crjens/PiPowerMeter/Documentation/ACIn.jpg

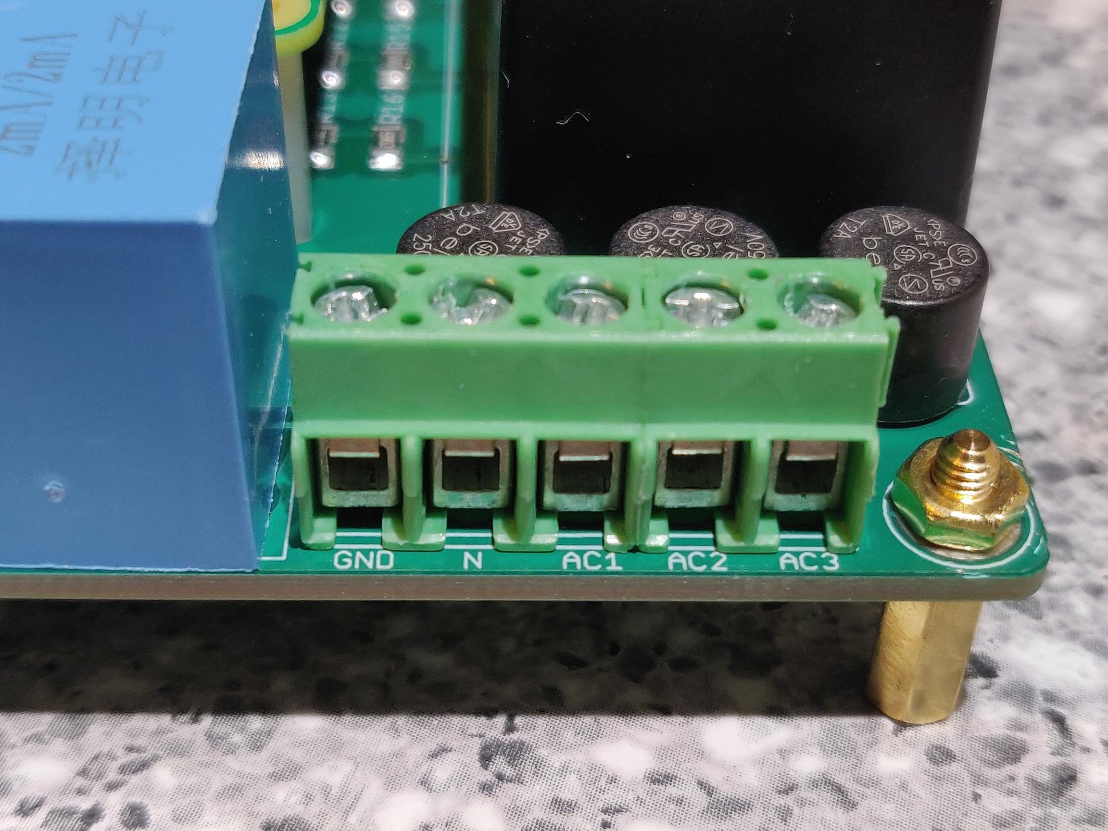
Documentation/ACIn.jpg
