crjens/PiPowerMeter/Documentation/boards.jpg

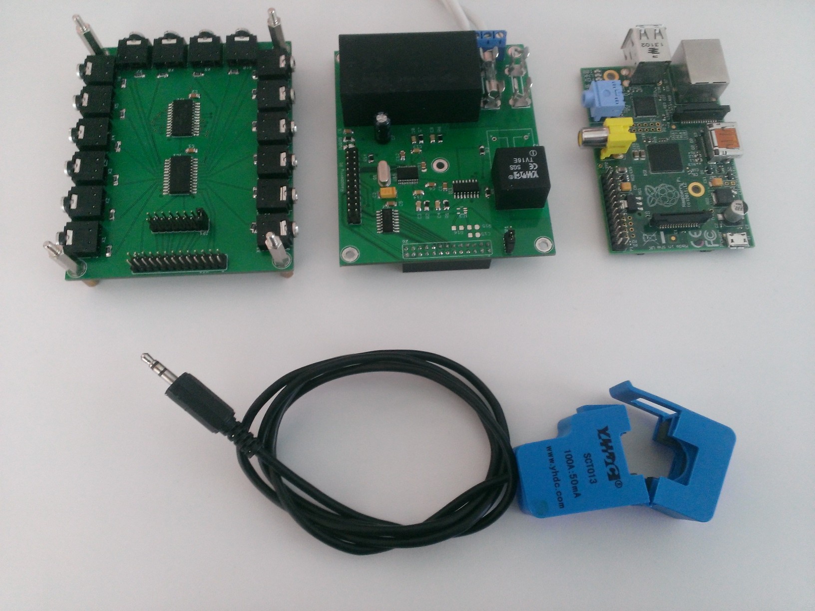
Documentation/boards.jpg
