crjens/PiPowerMeter/Documentation/DSC_0002.JPG

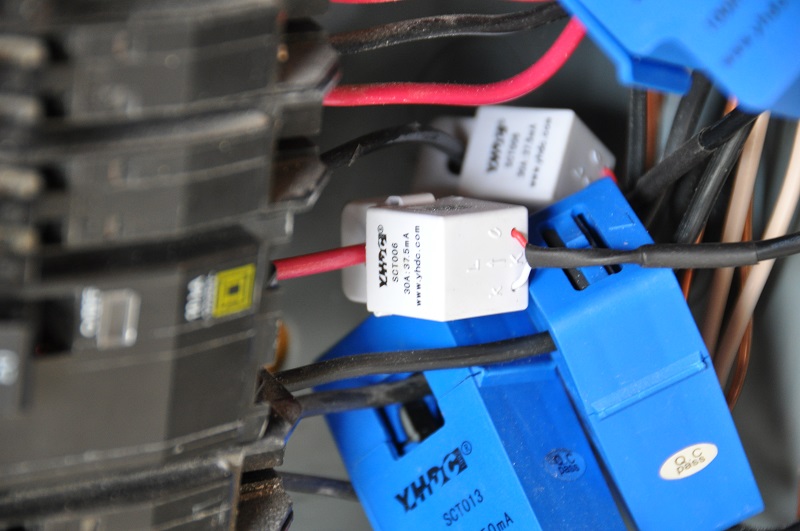
Documentation/DSC_0002.JPG
