crjens/PiPowerMeter/Documentation/DSC_0012.JPG

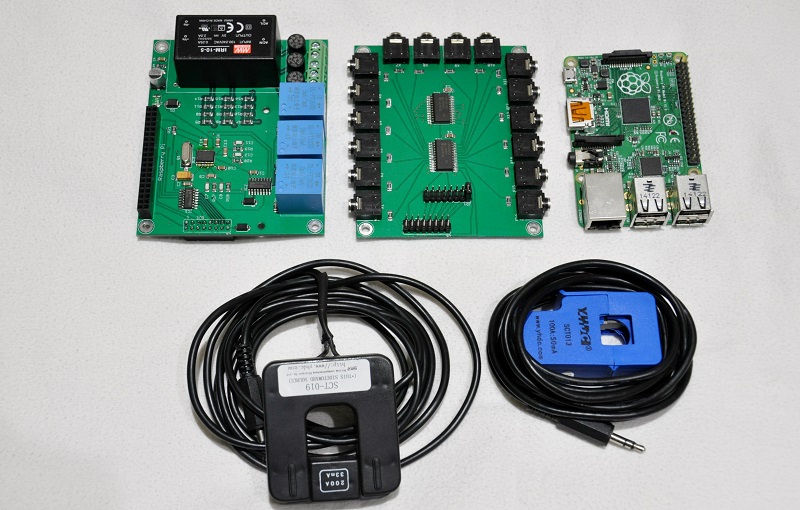
Documentation/DSC_0012.JPG
