crjens/PiPowerMeter/Documentation/DSC_0077.JPG

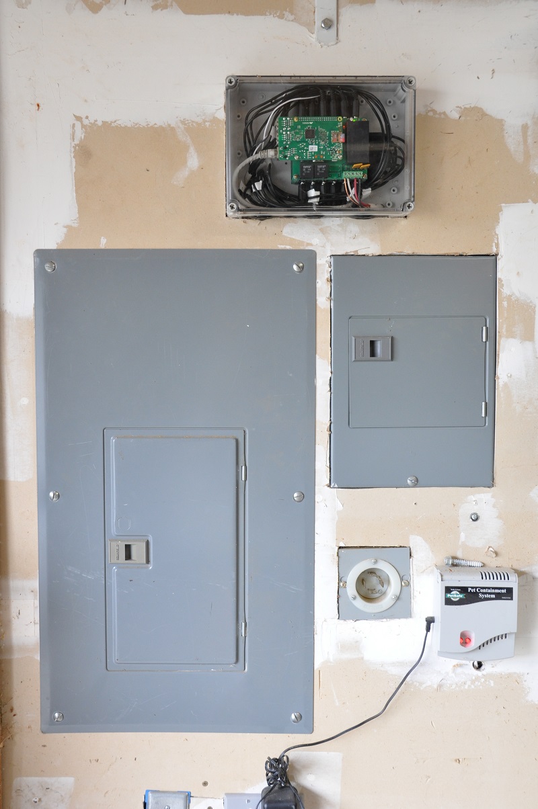
Documentation/DSC_0077.JPG
