crjens/PiPowerMeter/Documentation/DSC_0078.JPG

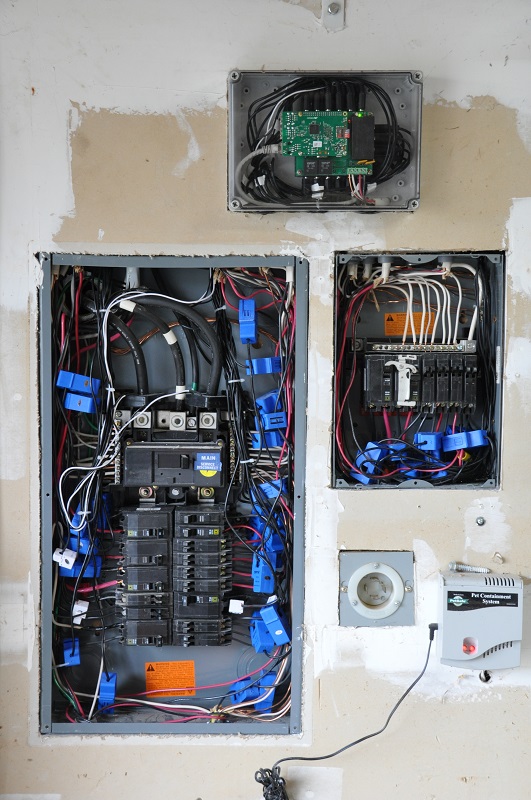
Documentation/DSC_0078.JPG
