crjens/PiPowerMeter/Documentation/main.png

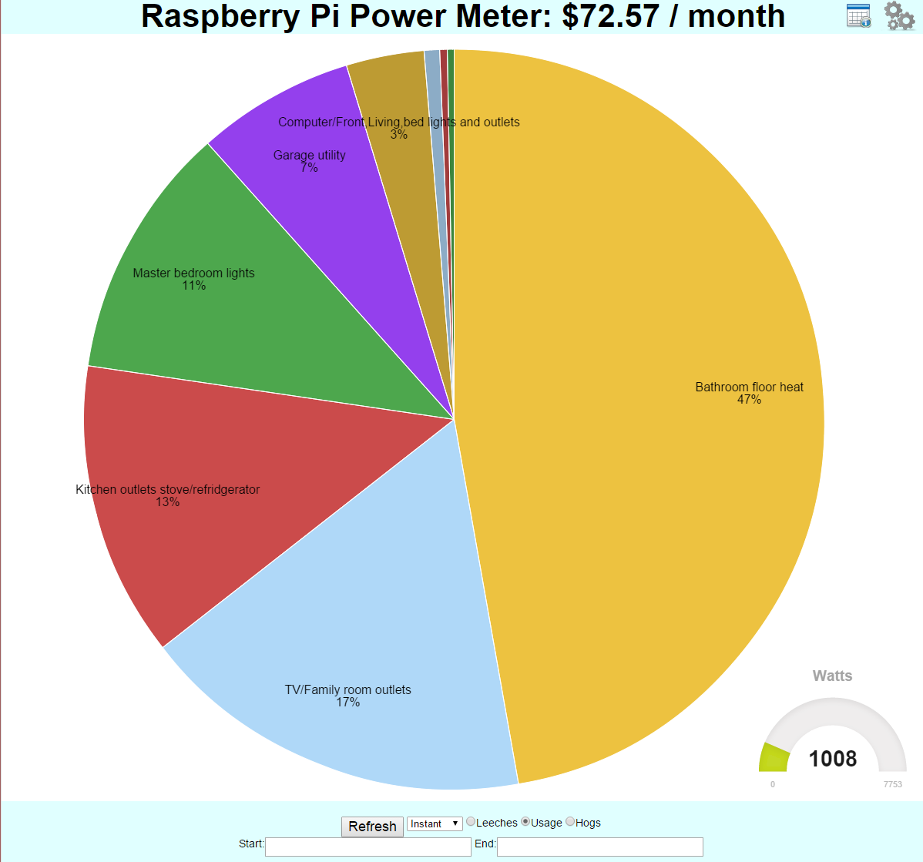
Documentation/main.png
