crjens/PiPowerMeter/Eagle/V4.0/PowerMeter.brd.png

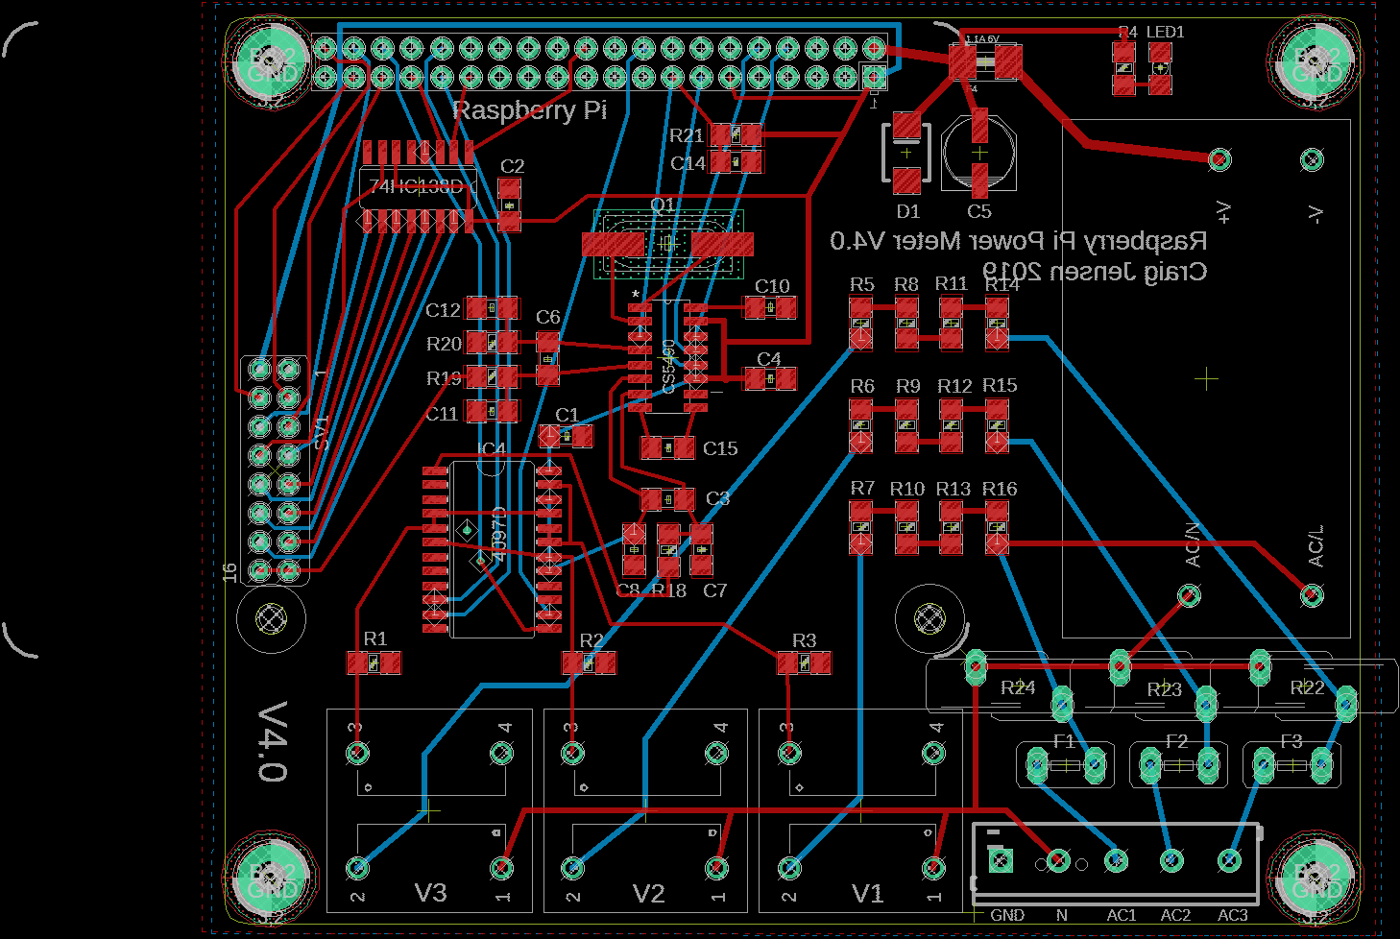
Eagle/V4.0/PowerMeter.brd.png
