crjens/PiPowerMeter/Eagle/V4.0/PowerMeter.sch.png

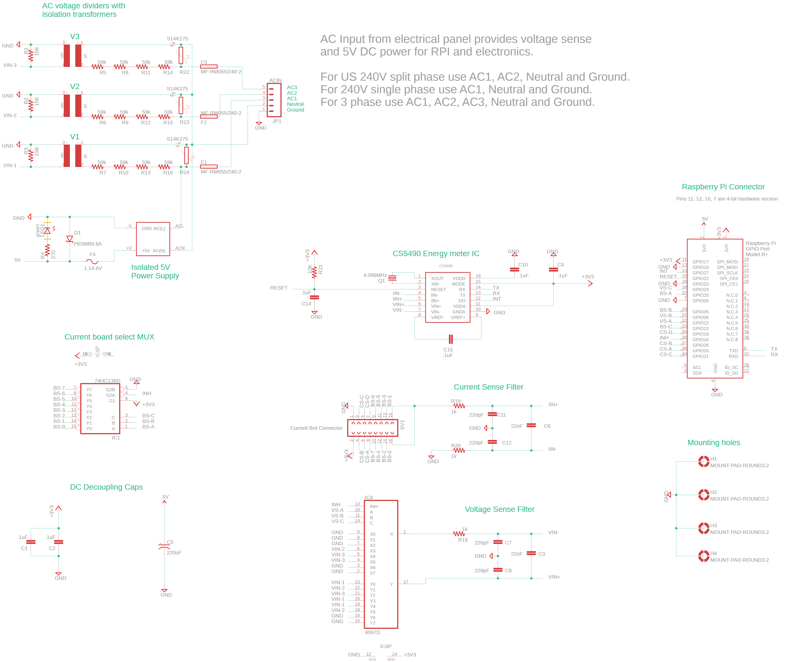
Eagle/V4.0/PowerMeter.sch.png
