crjens/PiPowerMeter/Eagle/V4.0/PowerMeterCurrent.brd.png

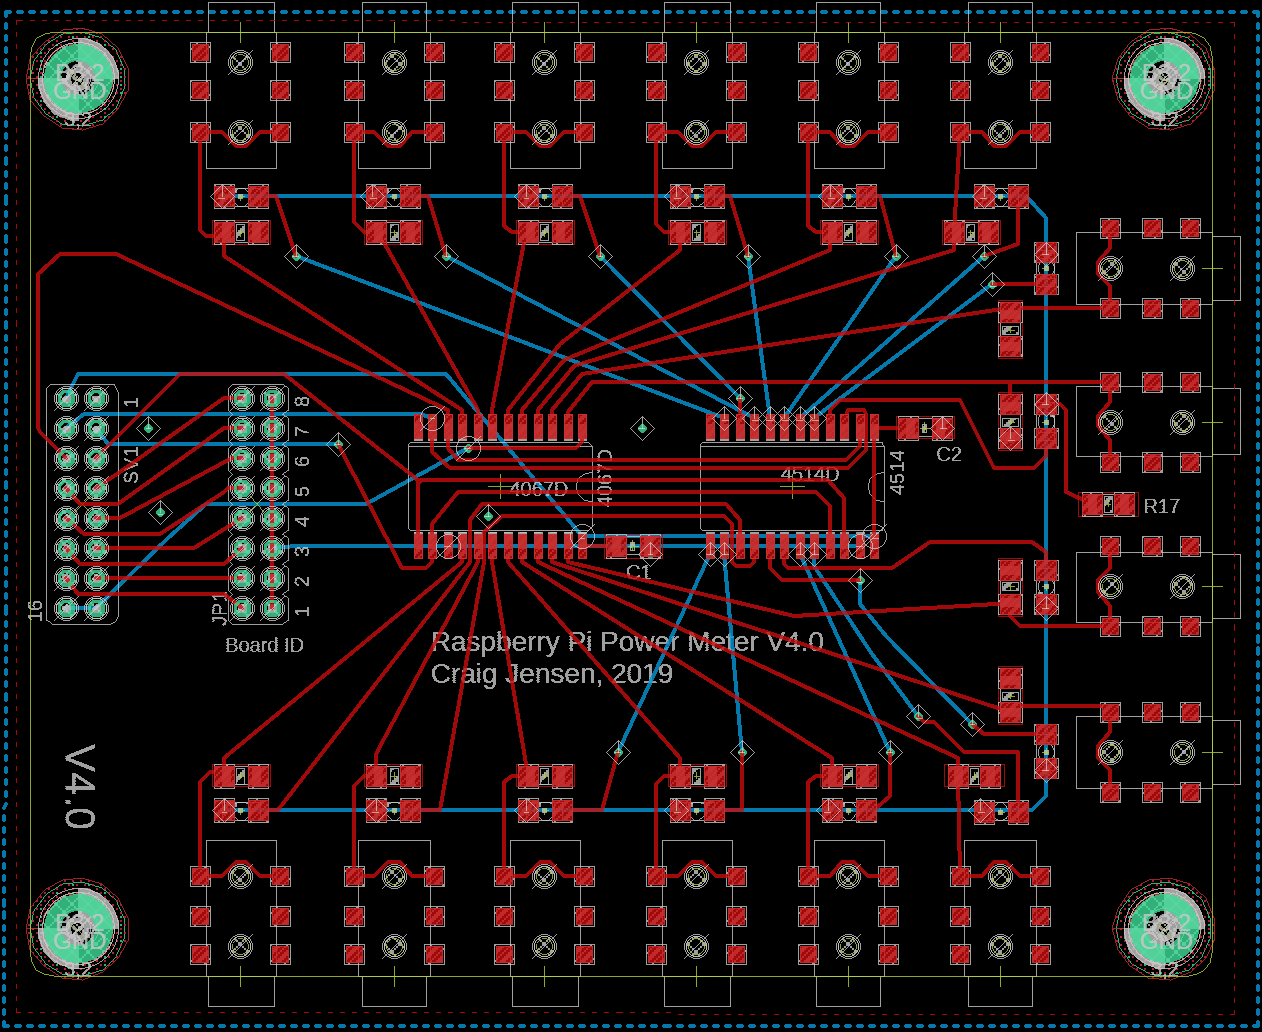
Eagle/V4.0/PowerMeterCurrent.brd.png
