crjens/PiPowerMeter/Eagle/V4.0/PowerMeterCurrent.sch.png

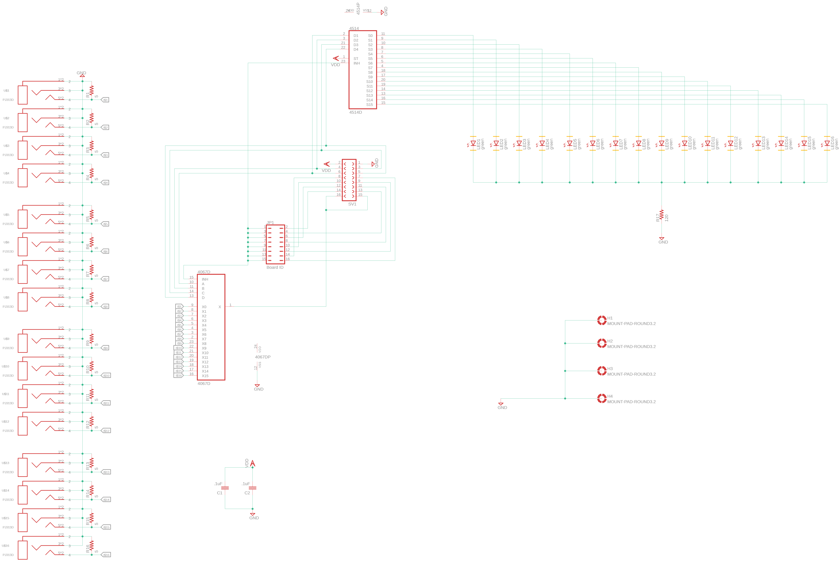
Eagle/V4.0/PowerMeterCurrent.sch.png
